knack-tactical/GAL/.ref/PCB Wire Diagram.png

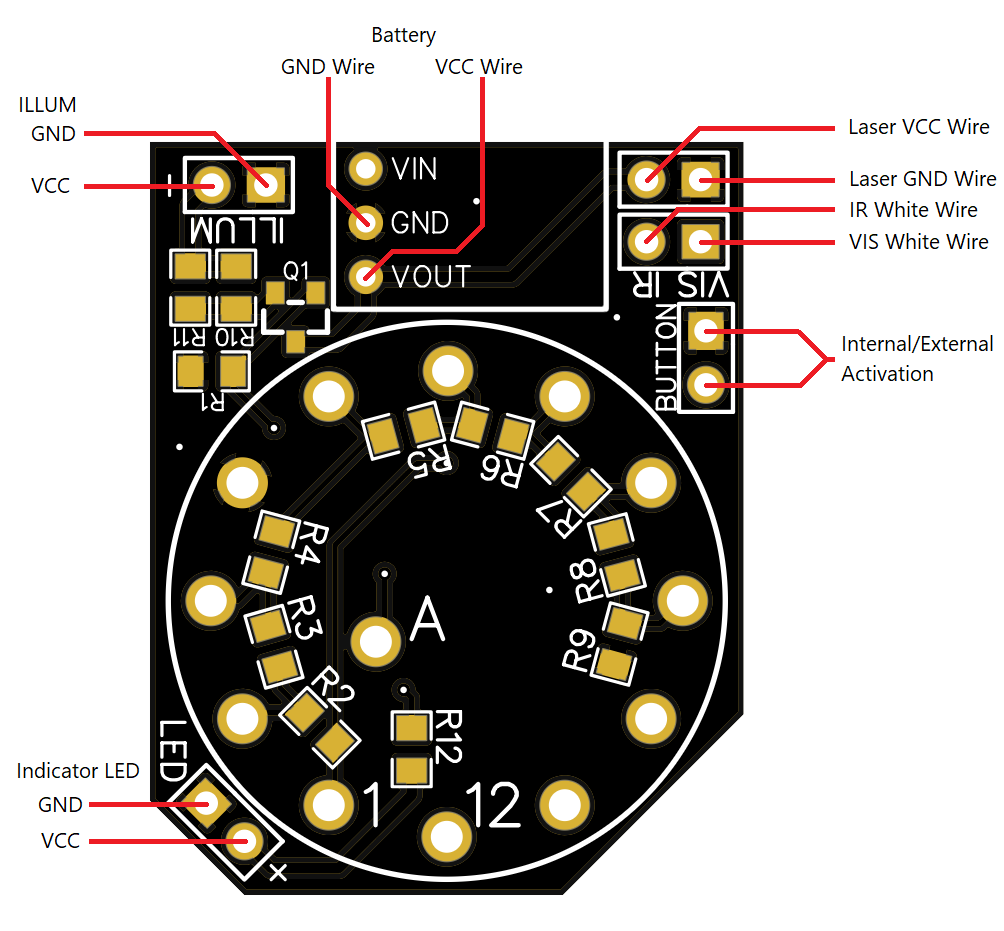
.ref/PCB Wire Diagram.png
