knack-tactical/GAL/attiny_program/Tools_settings.png

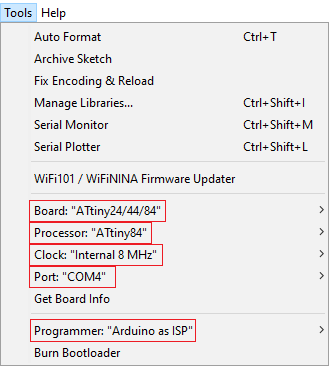
attiny_program/Tools_settings.png
