knack-tactical/GAL/RENDER/GAL_top.png

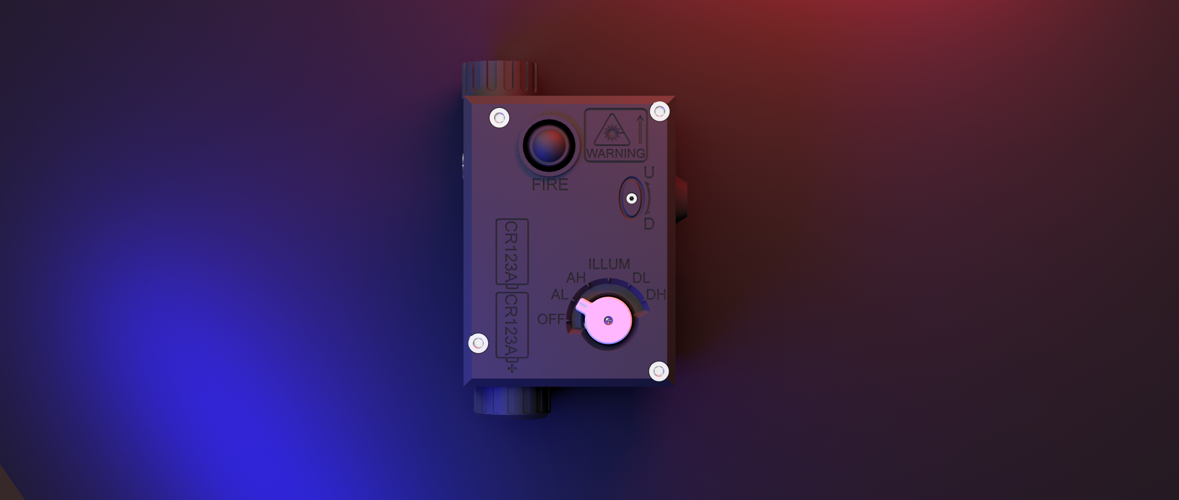
RENDER/GAL_top.png
