knack-tactical/GAL/Renders/2.png

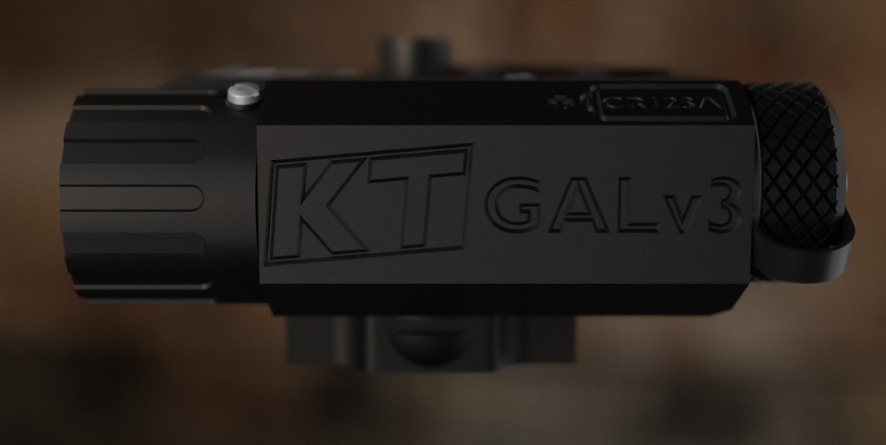
Renders/2.png
