knack-tactical/GAL/Renders/3.png

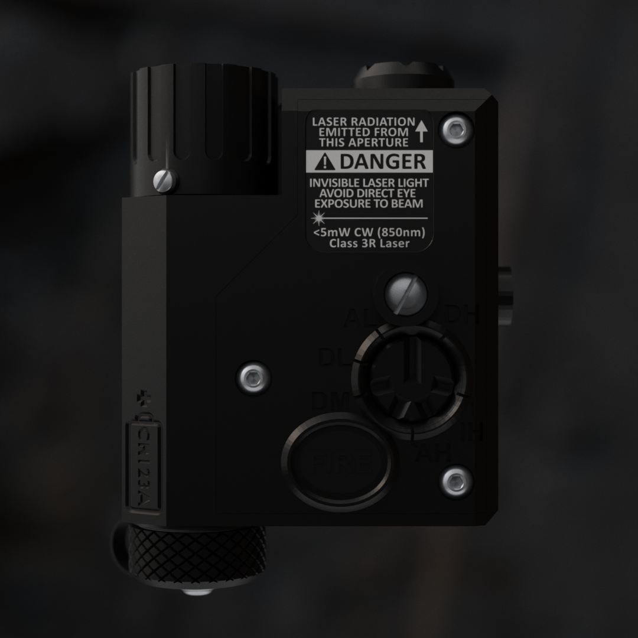
Renders/3.png
