knack-tactical/GAL/Renders/4.JPG

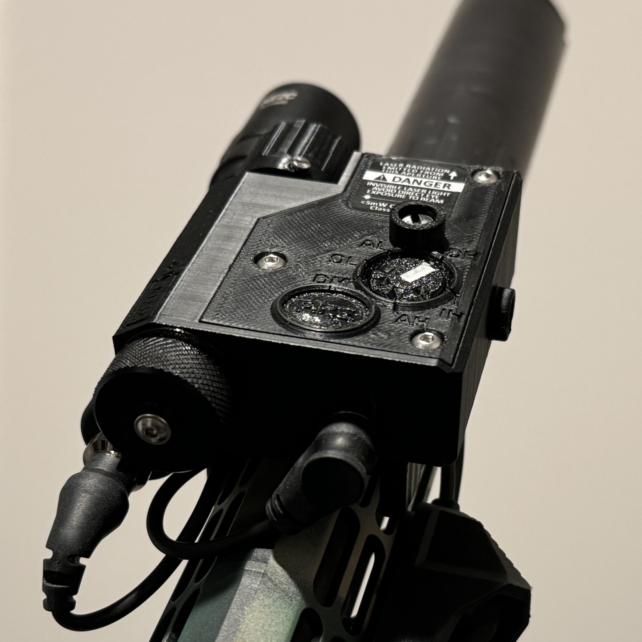
Renders/4.JPG
