knack-tactical/GAL/Renders/5.JPG

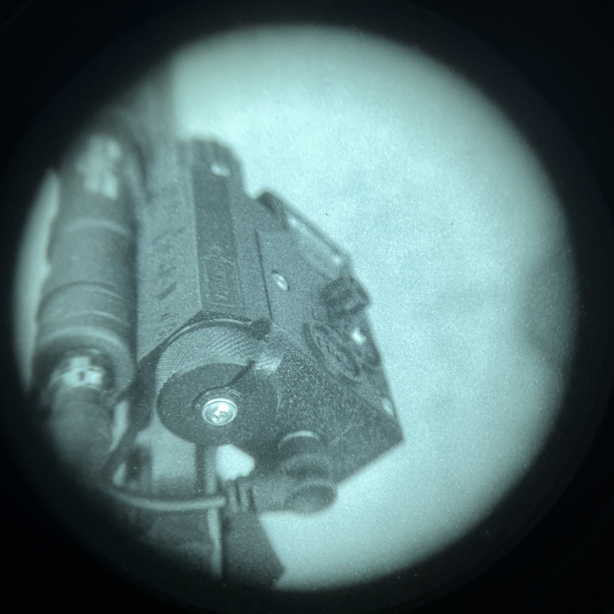
Renders/5.JPG
