knack-tactical/GAL/Renders/6.JPG

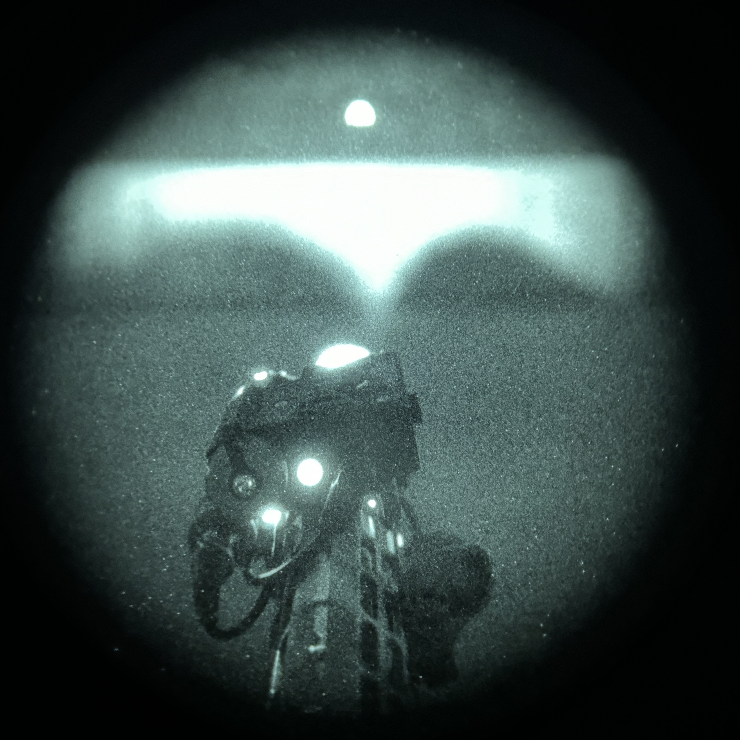
Renders/6.JPG
