knack-tactical/GAL/Renders/front_angle_warehouse.png

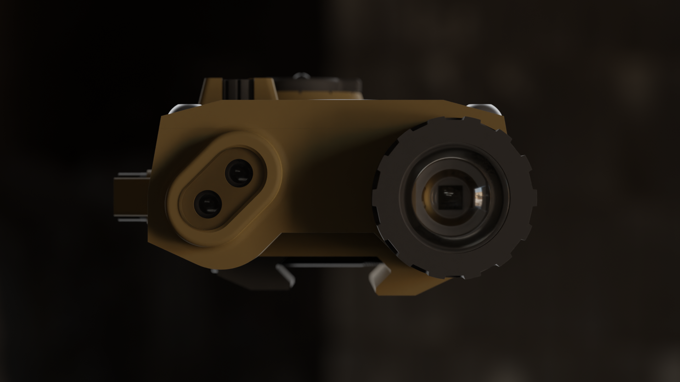
Renders/front_angle_warehouse.png
