knack-tactical/GAL/Renders/front_dark.png

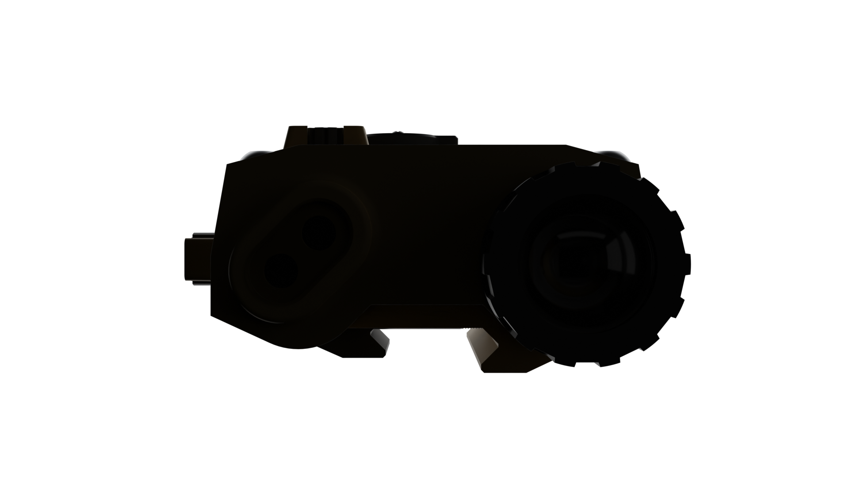
Renders/front_dark.png
