knack-tactical/GAL/Renders/illum_angle_warehouse.png

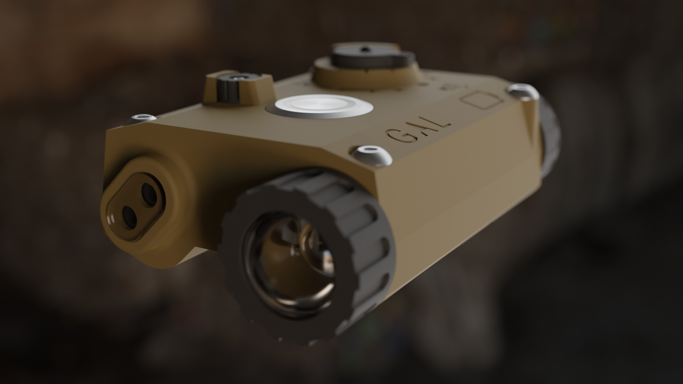
Renders/illum_angle_warehouse.png
