knack-tactical/GAL/Renders/render.png

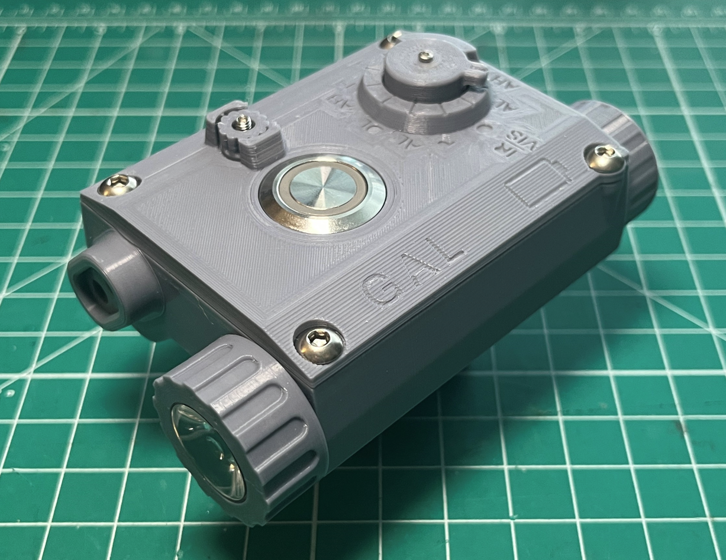
Renders/render.png
