knack-tactical/GAL/Machined Parts Drawings/battery_cap.PNG

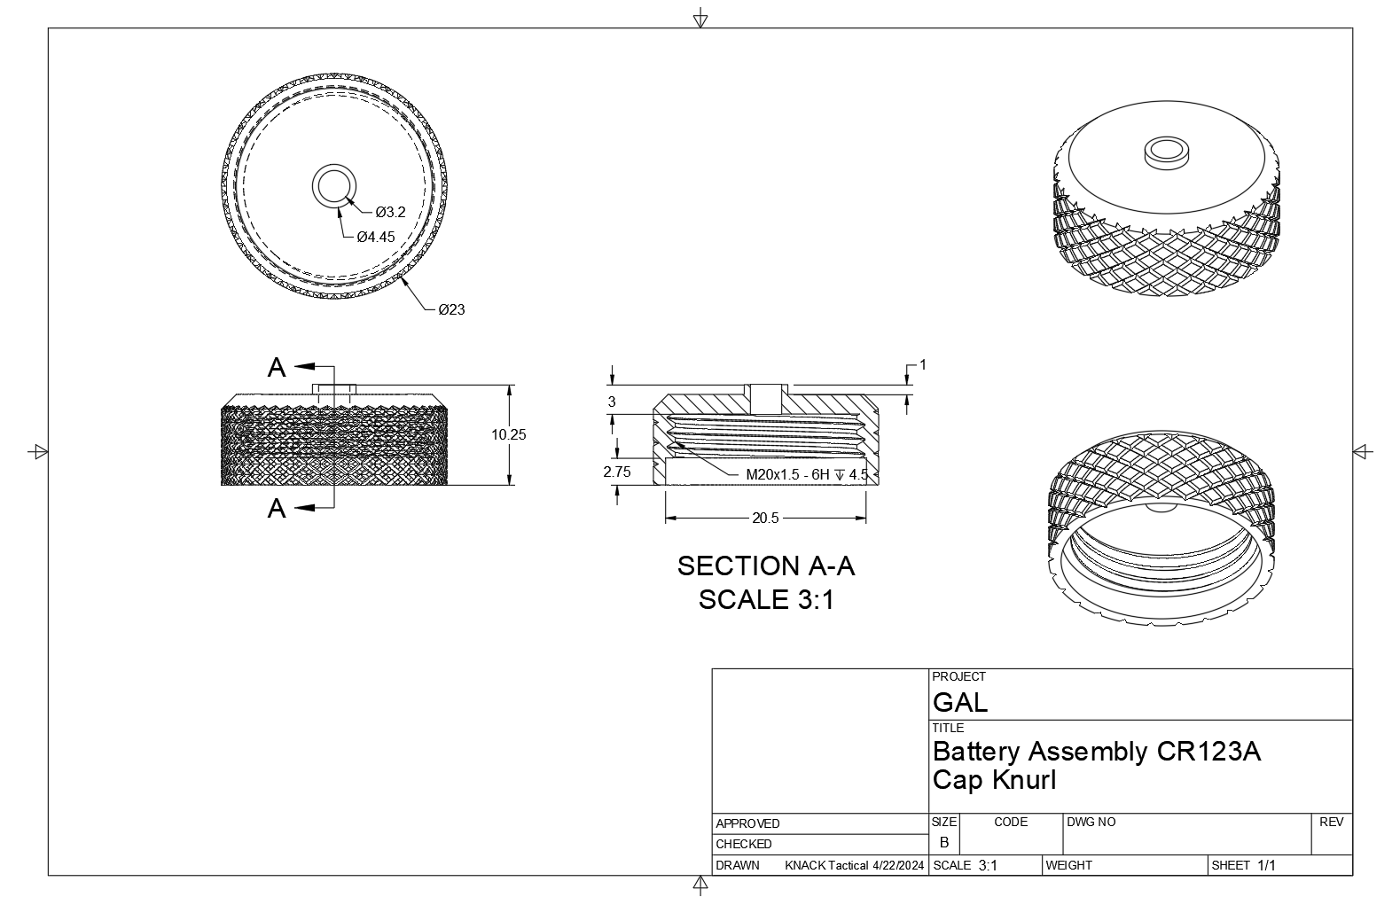
Machined Parts Drawings/battery_cap.PNG
