knack-tactical/GAL/Machined Parts Drawings/battery_tube.PNG

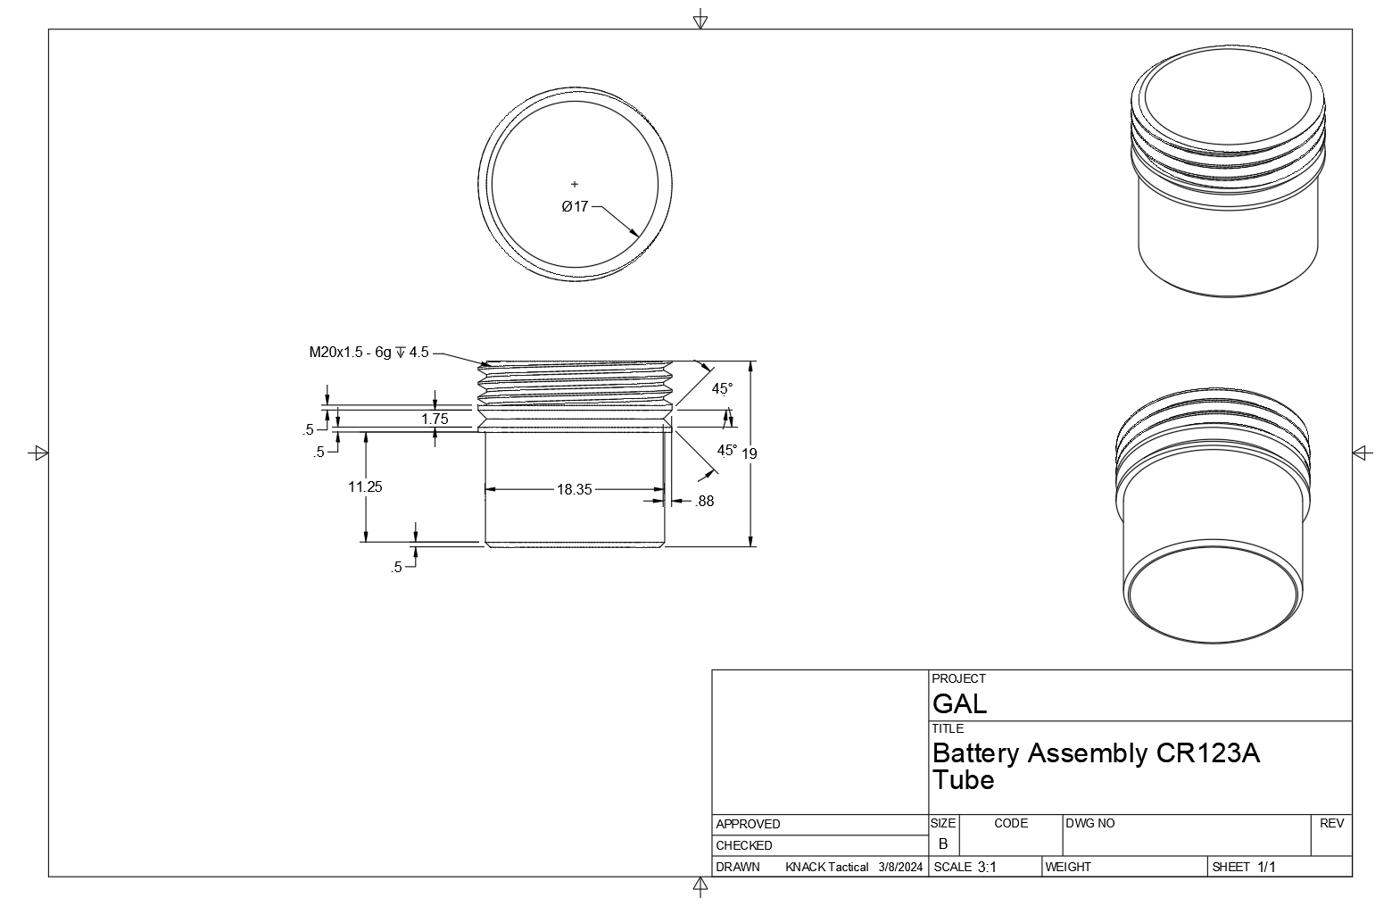
Machined Parts Drawings/battery_tube.PNG
