knack-tactical/GAL/Machined Parts Drawings/crane_port_stage_1.PNG

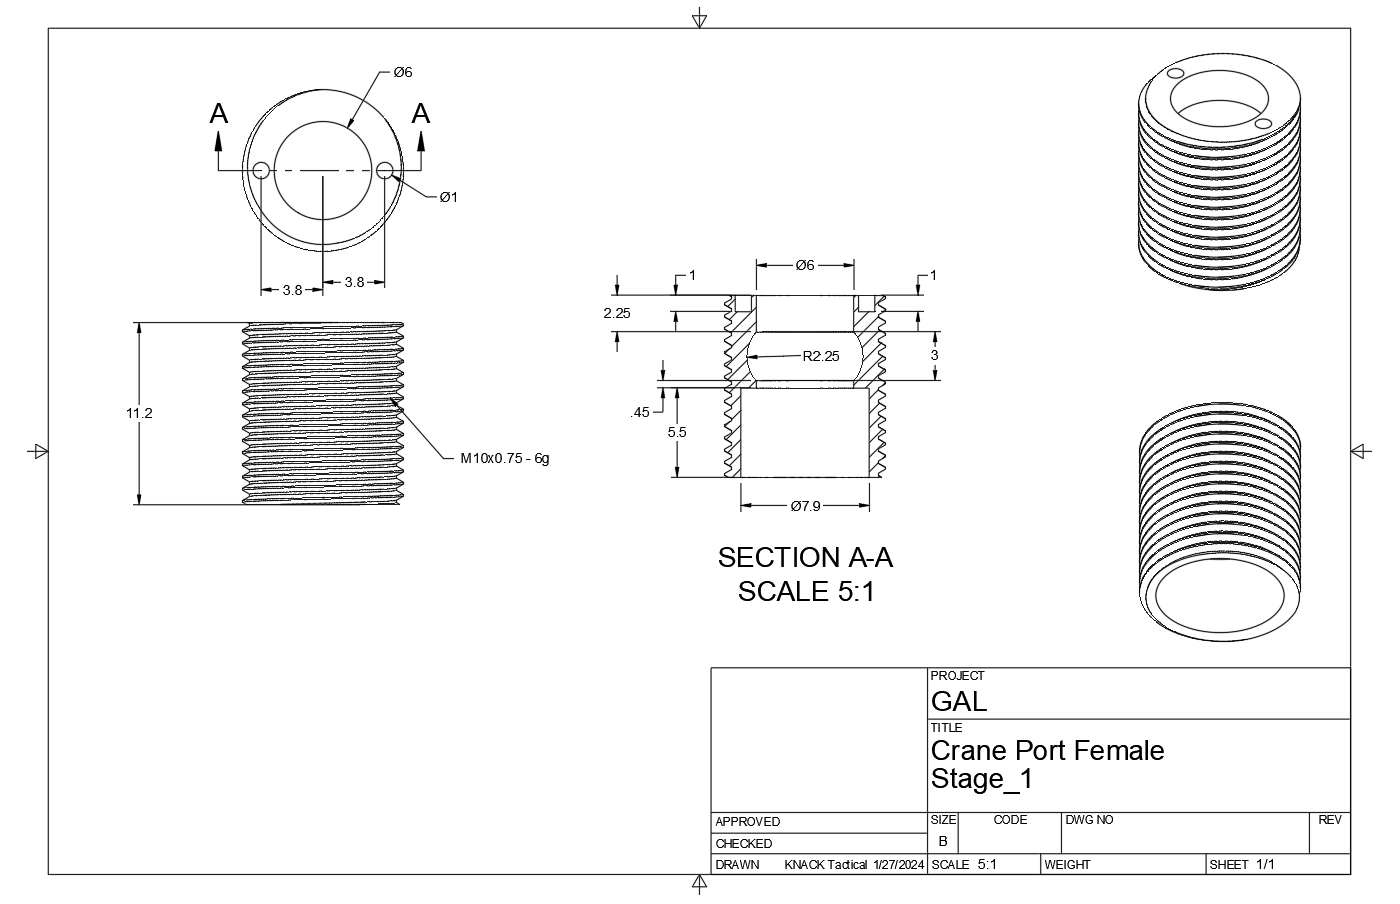
Machined Parts Drawings/crane_port_stage_1.PNG
