knack-tactical/GAL/Machined Parts Drawings/crane_port_stage_2.PNG

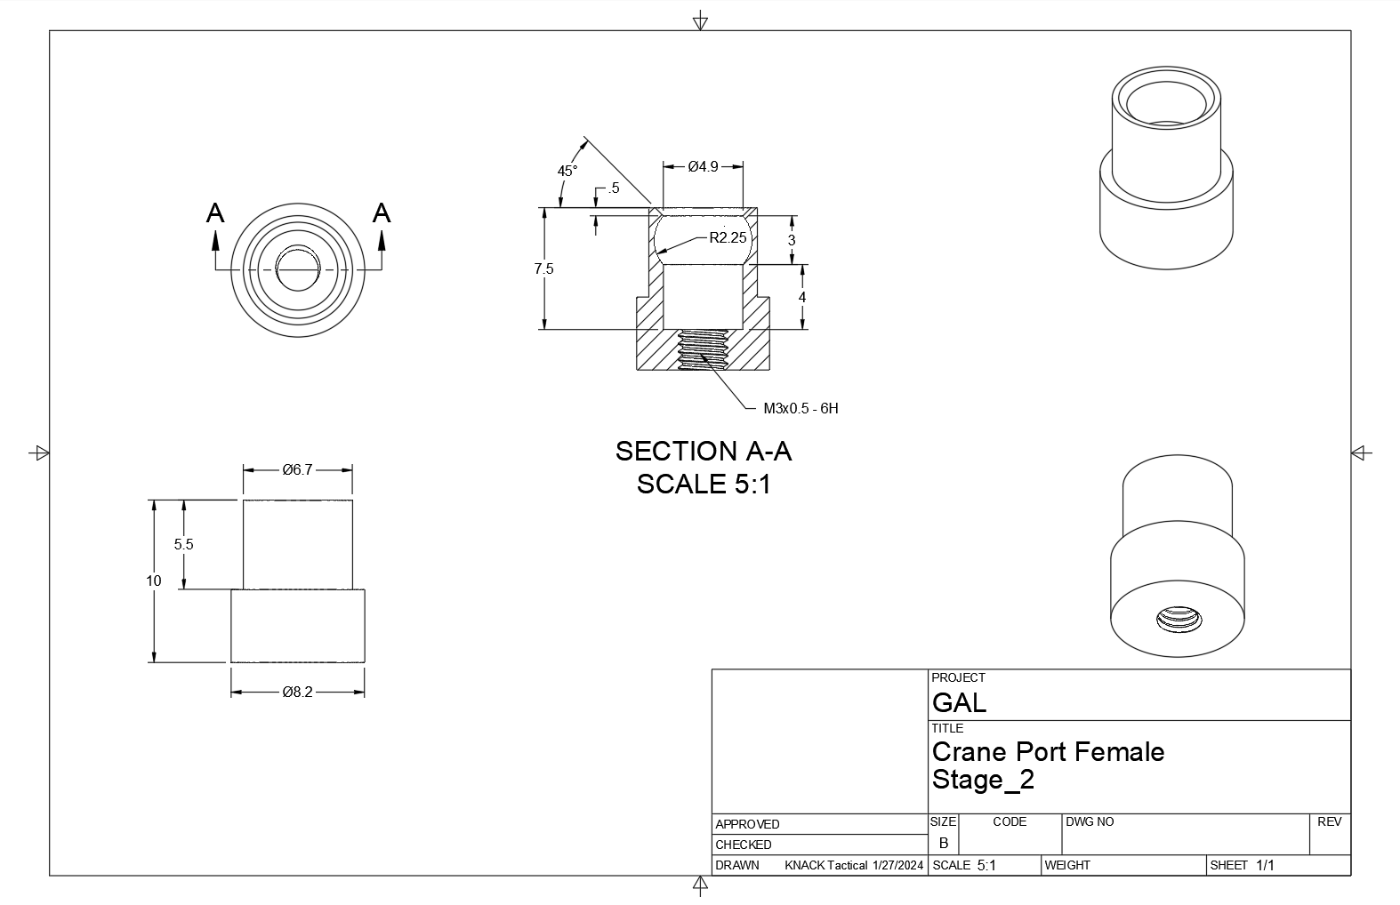
Machined Parts Drawings/crane_port_stage_2.PNG
