knack-tactical/GAL/STL/community_mods/mod_03_selector_knob.stl

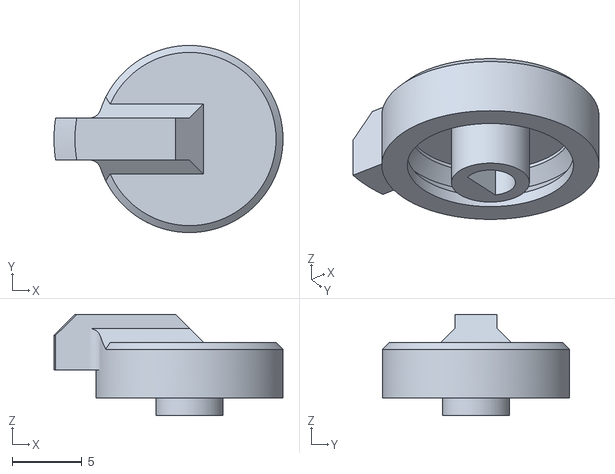
[picture p38: CAD file, 2024-10-04]
STL/community_mods/mod_03_selector_knob.stl
16.4 x 13.4 x 7.25
