knack-tactical/GAL/STEP/edits_by_zb/GAL_battery_cap_retention_zb.step

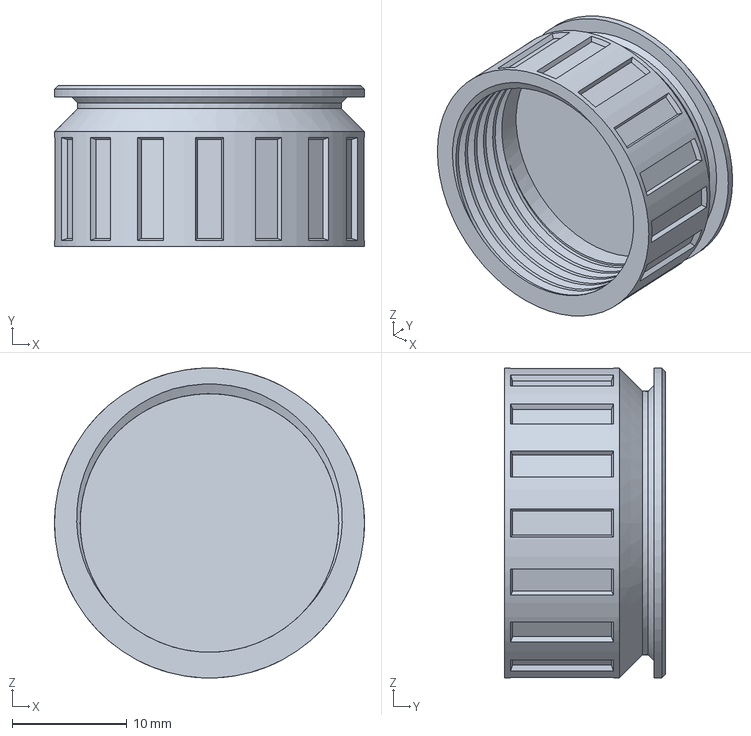
[picture p39: CAD file, 2023-12-14]
STEP/edits_by_zb/GAL_battery_cap_retention_zb.step
27.0 x 14.0 x 27.0 mm
