knack-tactical/GAL/STL/07_crane_port_spacer.stl

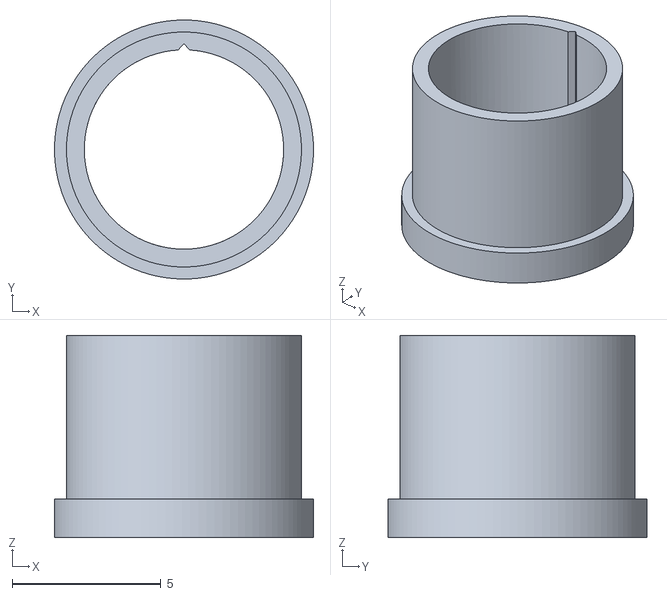
[picture p40: CAD file, 2024-07-04]
STL/07_crane_port_spacer.stl
8.71 x 8.71 x 6.80
