knack-tactical/GAL/STEP/edits_by_zb/GAL_TPU_gaskets_retention_zb.step

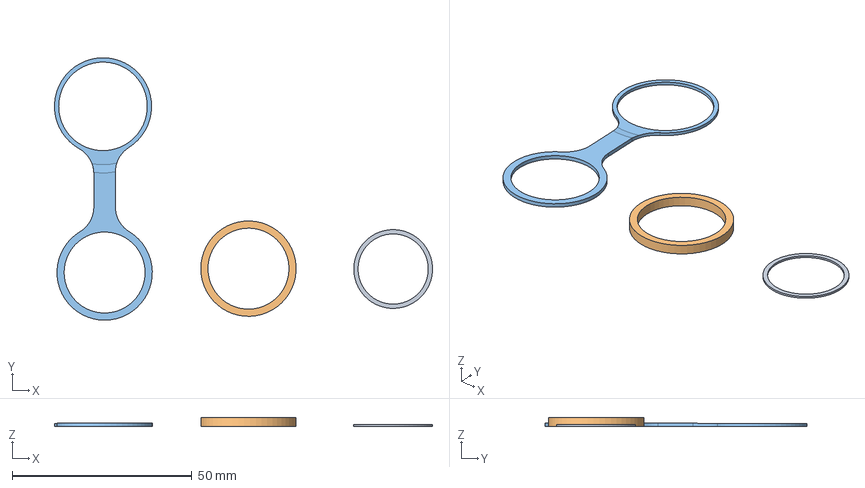
[picture p41: CAD file, 2023-12-14]
STEP/edits_by_zb/GAL_TPU_gaskets_retention_zb.step
105.0 x 72.9 x 2.50 mm
