knack-tactical/GAL/STL/community_mods/mod_01_selector_knob_zb.stl

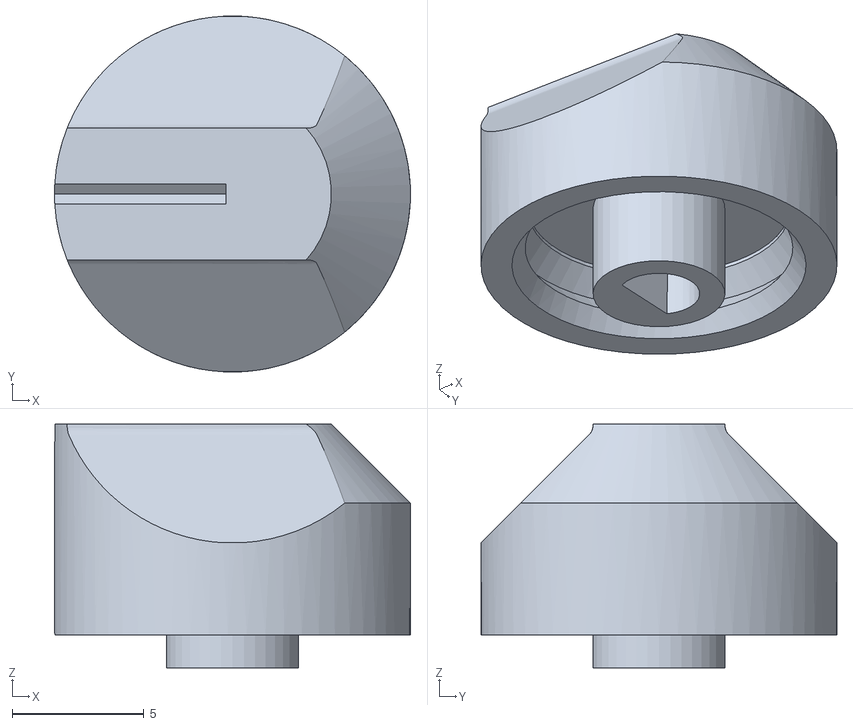
[picture p42: CAD file, 2024-08-01]
STL/community_mods/mod_01_selector_knob_zb.stl
13.5 x 13.5 x 9.25
