knack-tactical/GAL/STL/edits_by_zb/GAL_body_18650_crane_zb.stl

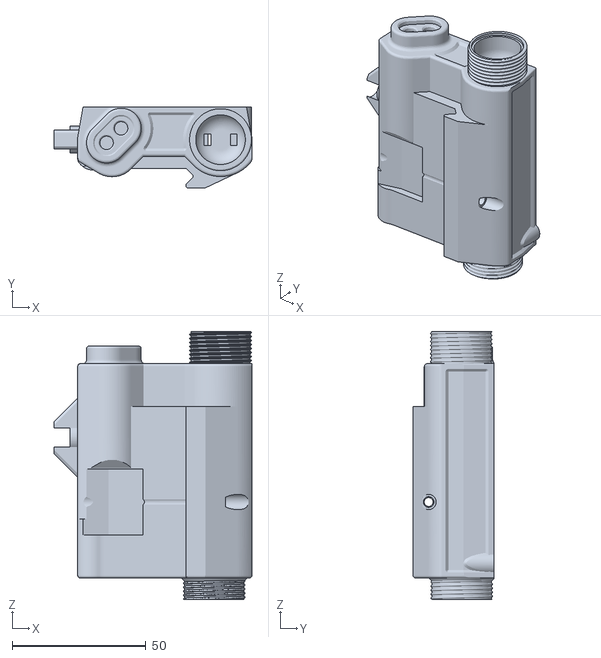
[picture p43: CAD file, 2023-12-15]
STL/edits_by_zb/GAL_body_18650_crane_zb.stl
73.8 x 30.2 x 100.0
