knack-tactical/GAL/STL/04_laser_lens_cap.stl

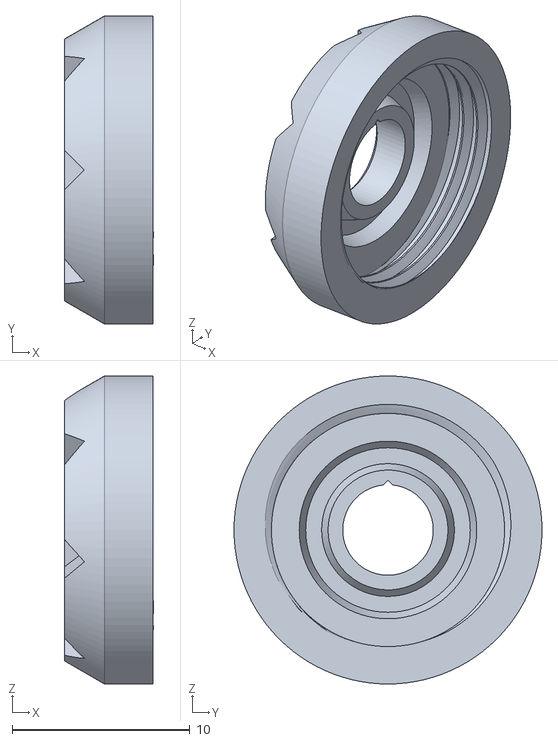
[picture p44: CAD file, 2024-07-03]
STL/04_laser_lens_cap.stl
5.02 x 17.3 x 17.3
