knack-tactical/GAL/STL/08_crane_port_installation_tool.stl

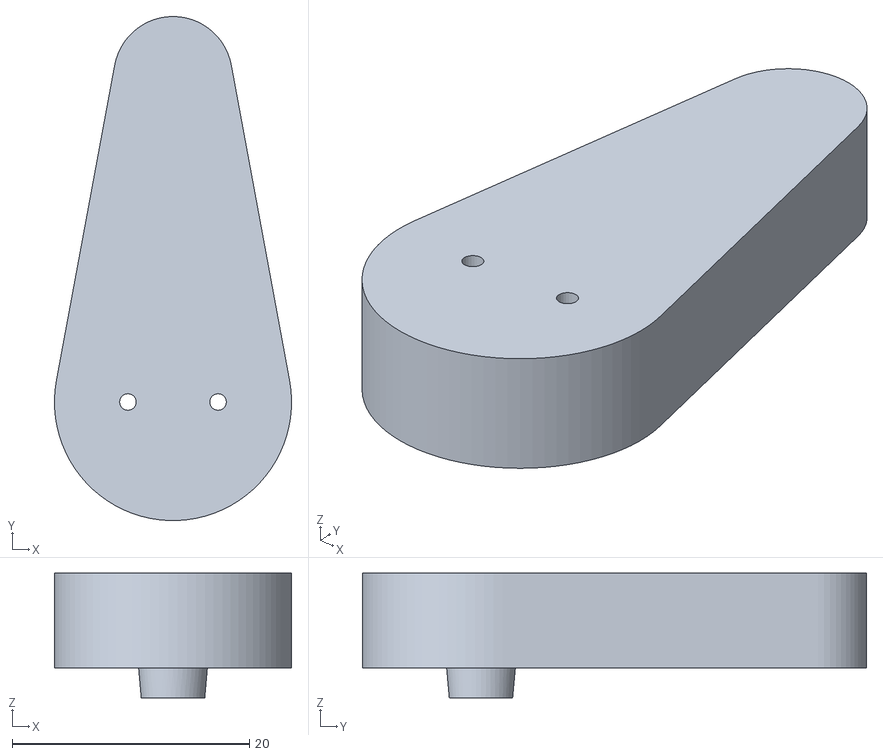
[picture p45: CAD file, 2024-07-03]
STL/08_crane_port_installation_tool.stl
20.0 x 42.5 x 10.5
