knack-tactical/GAL/STL/03_laser_housing.stl

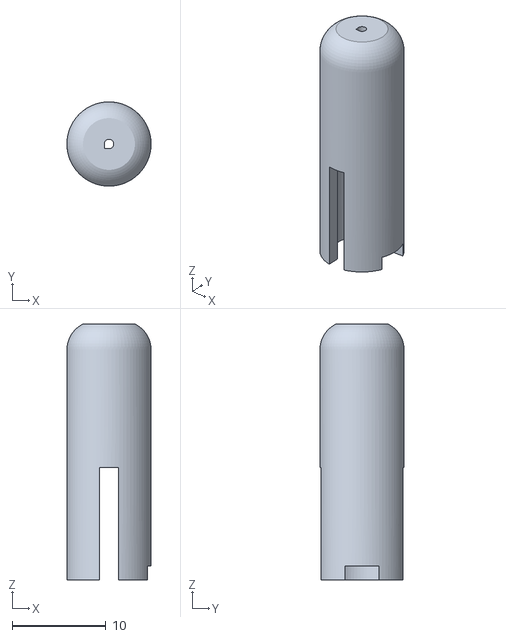
[picture p46: CAD file, 2024-07-03]
STL/03_laser_housing.stl
9.00 x 9.00 x 27.4
