knack-tactical/GAL/STL/09_battery_cap_retention_strap_TPU.stl

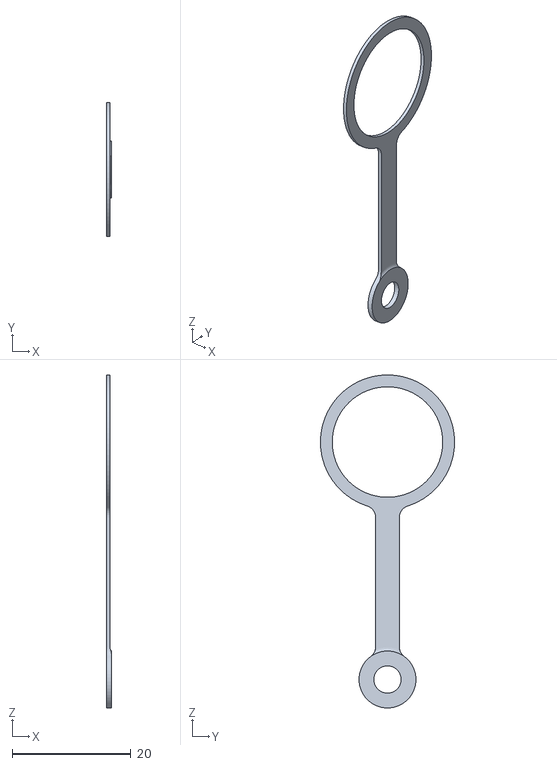
[picture p47: CAD file, 2024-07-03]
STL/09_battery_cap_retention_strap_TPU.stl
0.85 x 22.6 x 56.1
