knack-tactical/GAL/STL/02_laser_base.stl

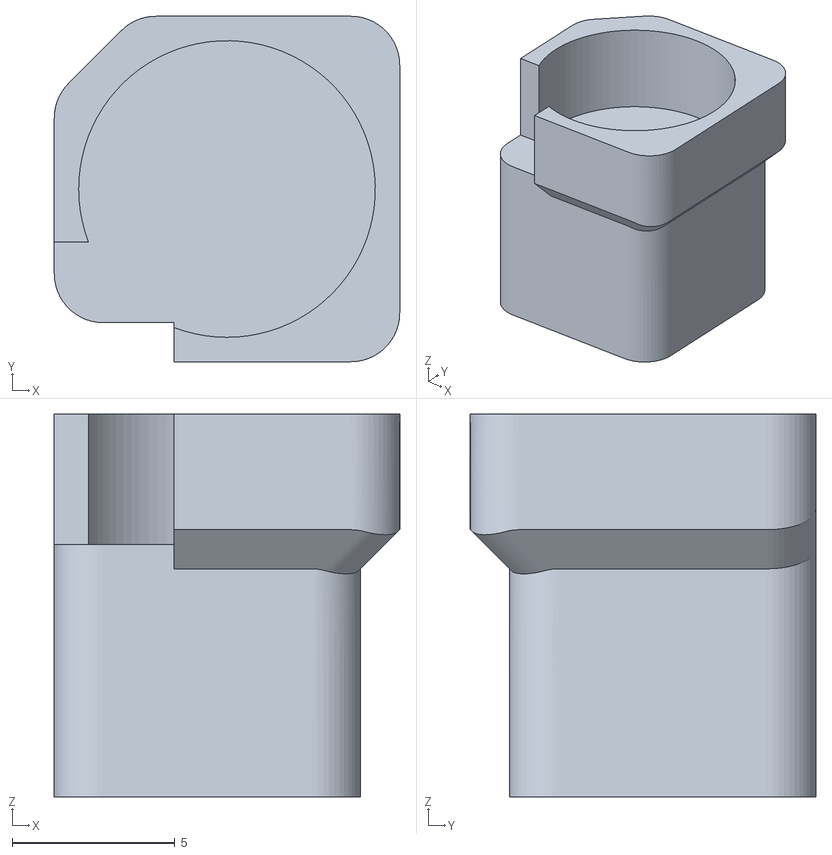
[picture p48: CAD file, 2024-07-03]
STL/02_laser_base.stl
10.6 x 10.6 x 11.8
