knack-tactical/GAL/STL/14_FIRE_button_TPU.stl

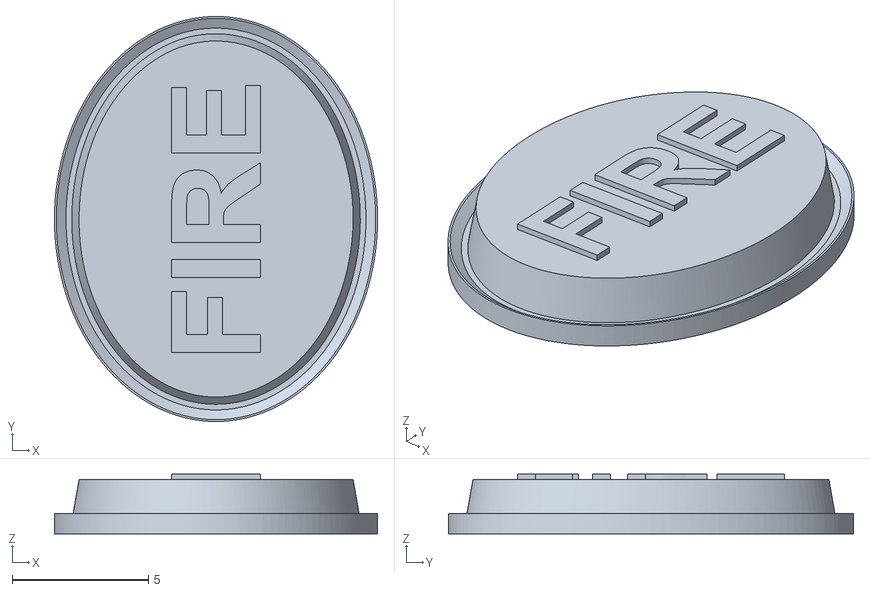
[picture p49: CAD file, 2024-07-03]
STL/14_FIRE_button_TPU.stl
11.9 x 14.9 x 2.20
