knack-tactical/GAL/STL/05_lens_cap.stl

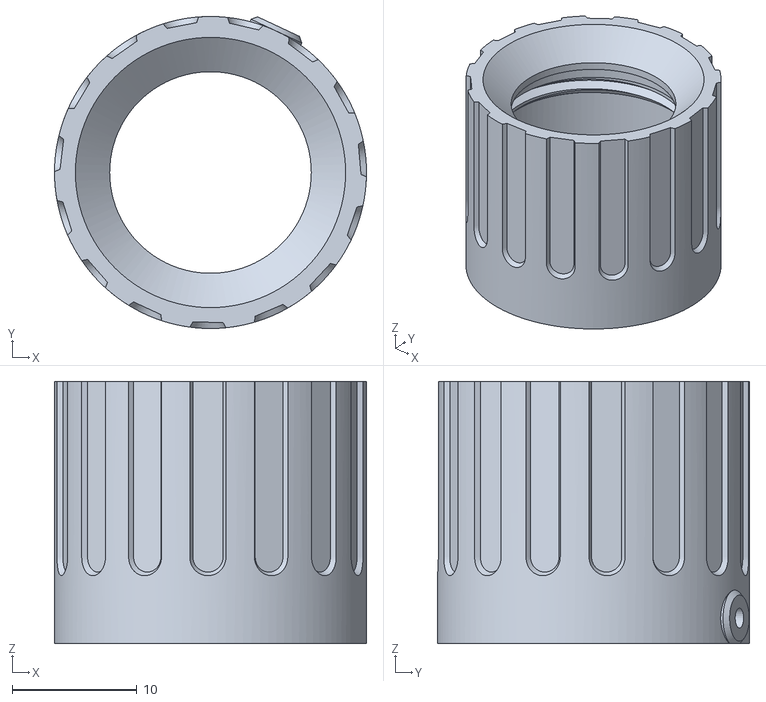
[picture p50: CAD file, 2024-07-03]
STL/05_lens_cap.stl
25.0 x 25.0 x 21.0
