knack-tactical/GAL/STL/13_button_retainer.stl

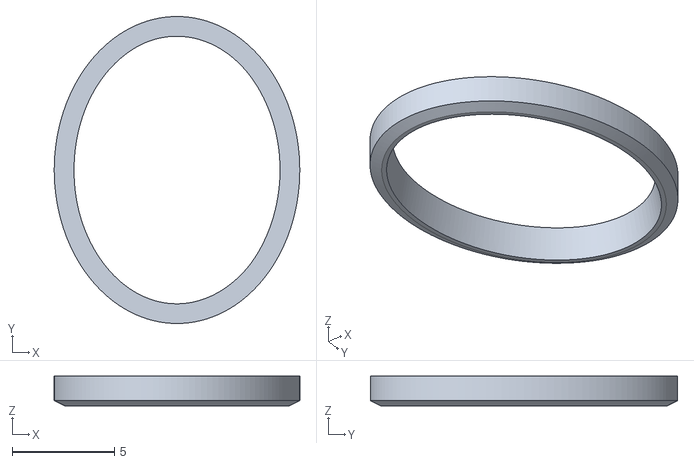
[picture p51: CAD file, 2024-07-03]
STL/13_button_retainer.stl
12.0 x 15.0 x 1.45
