knack-tactical/GAL/STL/06_lens_locking_ring.stl

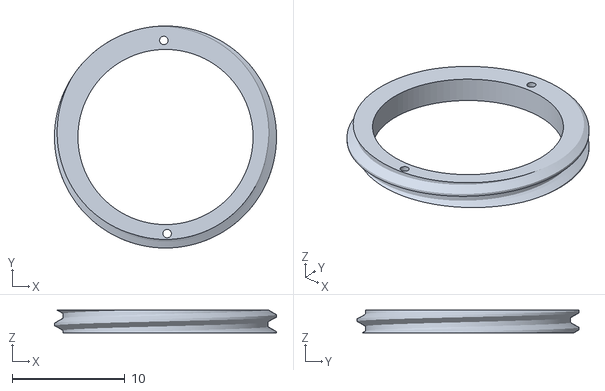
[picture p52: CAD file, 2024-07-03]
STL/06_lens_locking_ring.stl
19.6 x 19.6 x 2.00
