knack-tactical/GAL/STL/battery_cap.stl

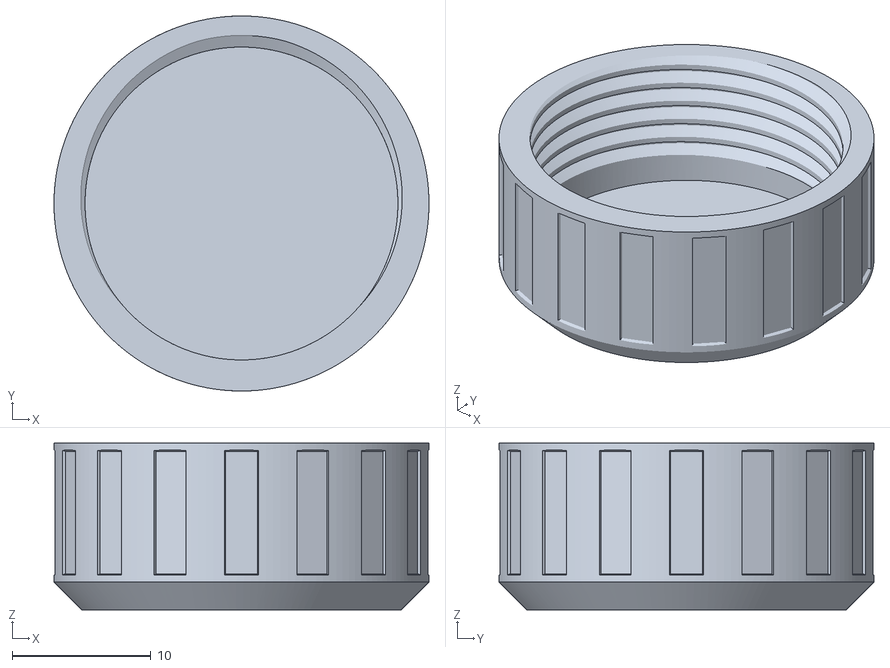
[picture p53: CAD file, 2023-12-23]
STL/battery_cap.stl
27.0 x 27.0 x 12.0
