knack-tactical/GAL/STL/vertical_adjustment_support.stl

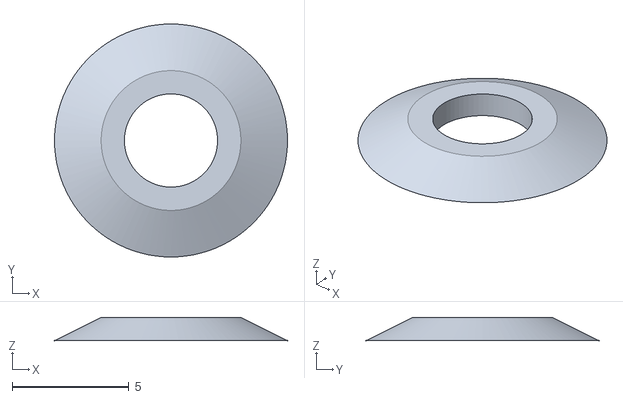
[picture p54: CAD file, 2023-10-02]
STL/vertical_adjustment_support.stl
10.0 x 10.0 x 1.00
