knack-tactical/GAL/STL/rotary_switch_jig.stl

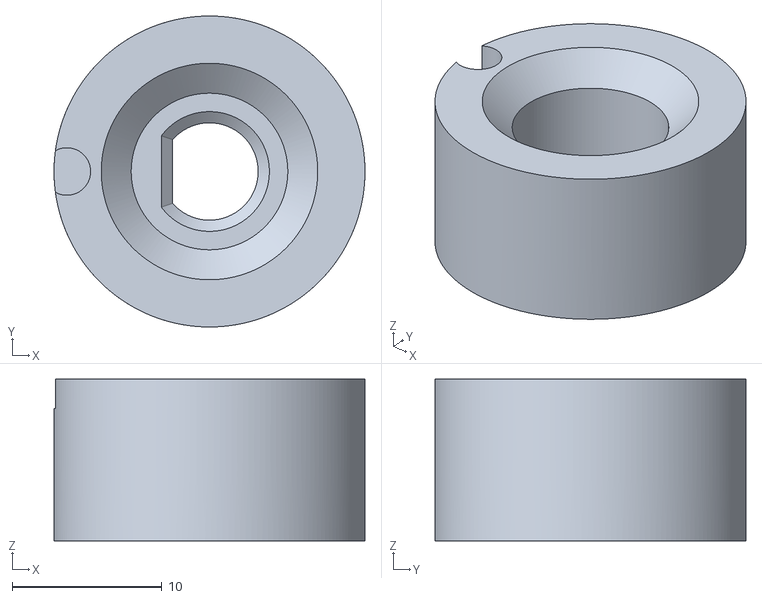
[picture p55: CAD file, 2023-10-02]
STL/rotary_switch_jig.stl
20.8 x 20.8 x 10.8
