knack-tactical/GAL/STL/adjustment_locking_knob.stl

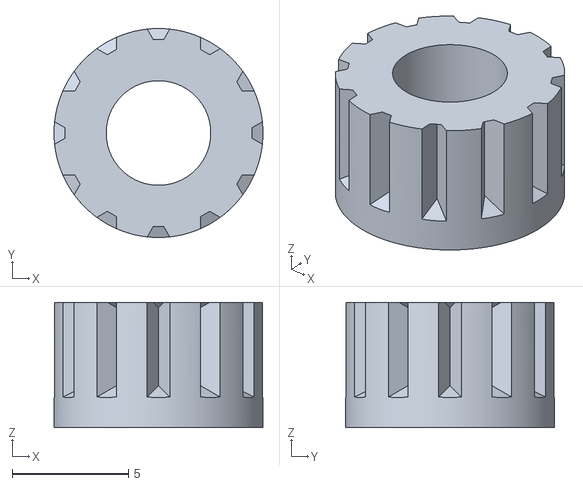
[picture p56: CAD file, 2023-10-02]
STL/adjustment_locking_knob.stl
9.00 x 9.00 x 5.40
