knack-tactical/GAL/STL/laser_hole_cover.dxf

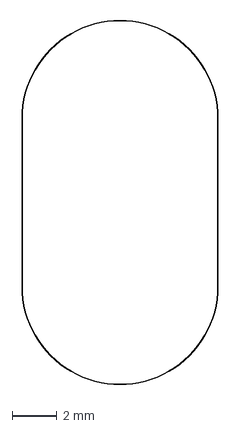
[picture p57: CAD file, 2023-10-02]
STL/laser_hole_cover.dxf
8.75 x 16.6 mm
