knack-tactical/GAL/STL/lid.stl

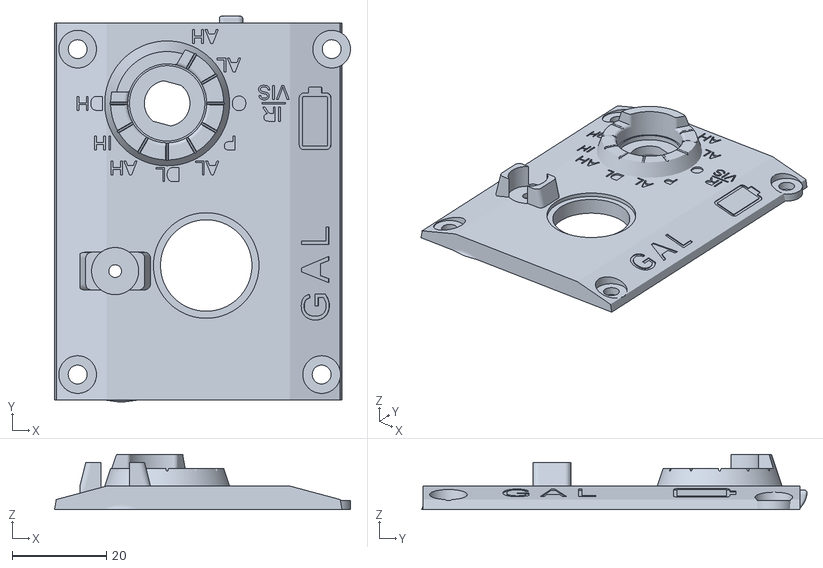
[picture p58: CAD file, 2023-10-02]
STL/lid.stl
62.8 x 81.9 x 11.8
