knack-tactical/GAL/STL/pic_rail_clamp.stl

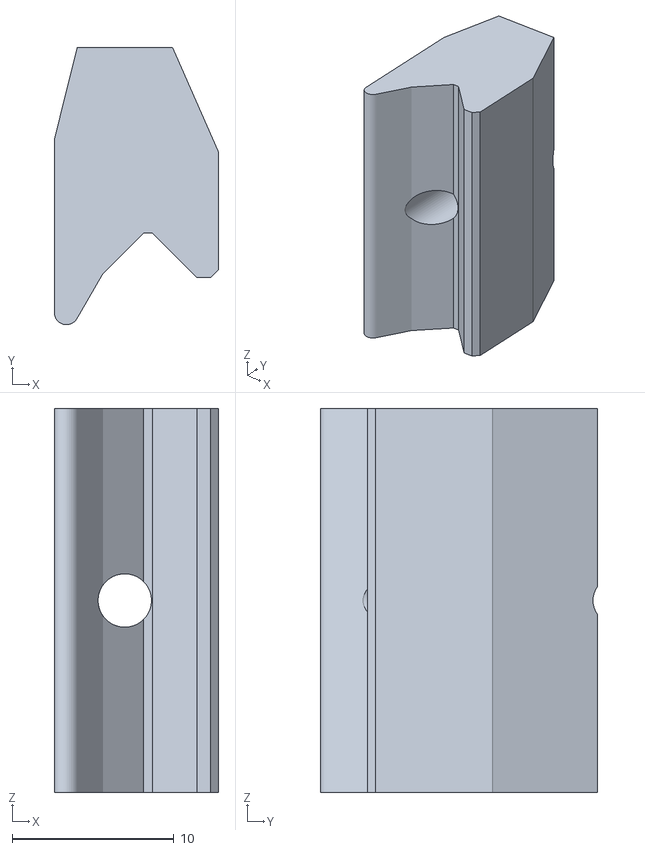
[picture p59: CAD file, 2023-10-02]
STL/pic_rail_clamp.stl
10.2 x 17.2 x 23.8
