knack-tactical/GAL/STL/Laser Body.stl

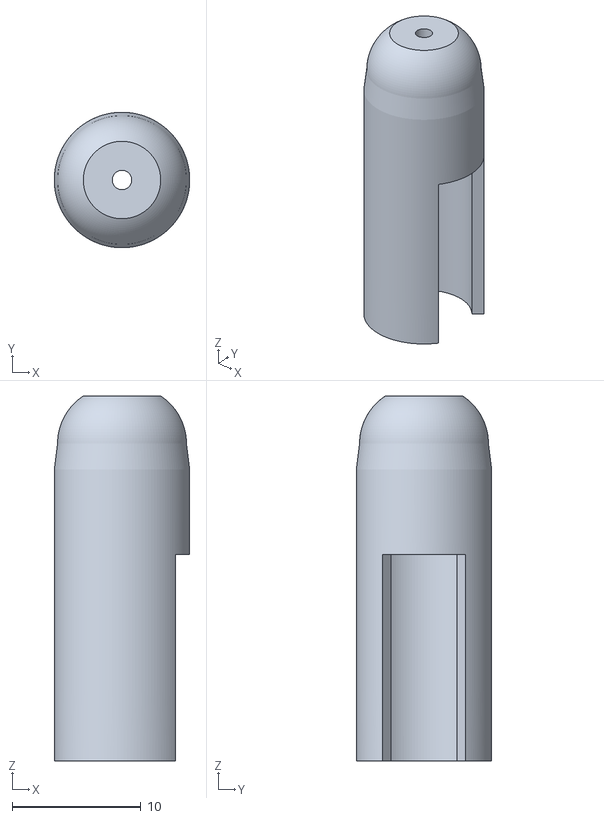
[picture p60: CAD file, 2023-03-20]
STL/Laser Body.stl
10.5 x 10.5 x 28.3
