knack-tactical/GAL/STL/Laser Base.stl

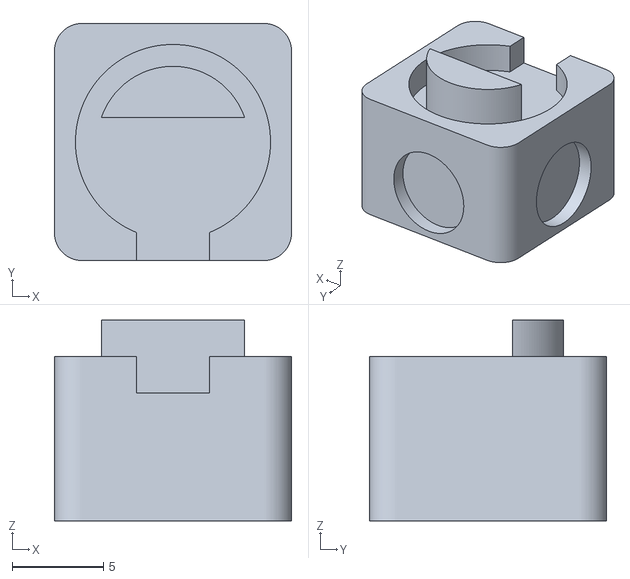
[picture p61: CAD file, 2023-03-20]
STL/Laser Base.stl
13.0 x 13.0 x 11.0
