knack-tactical/GAL/STL/GAL Rail Mount.stl

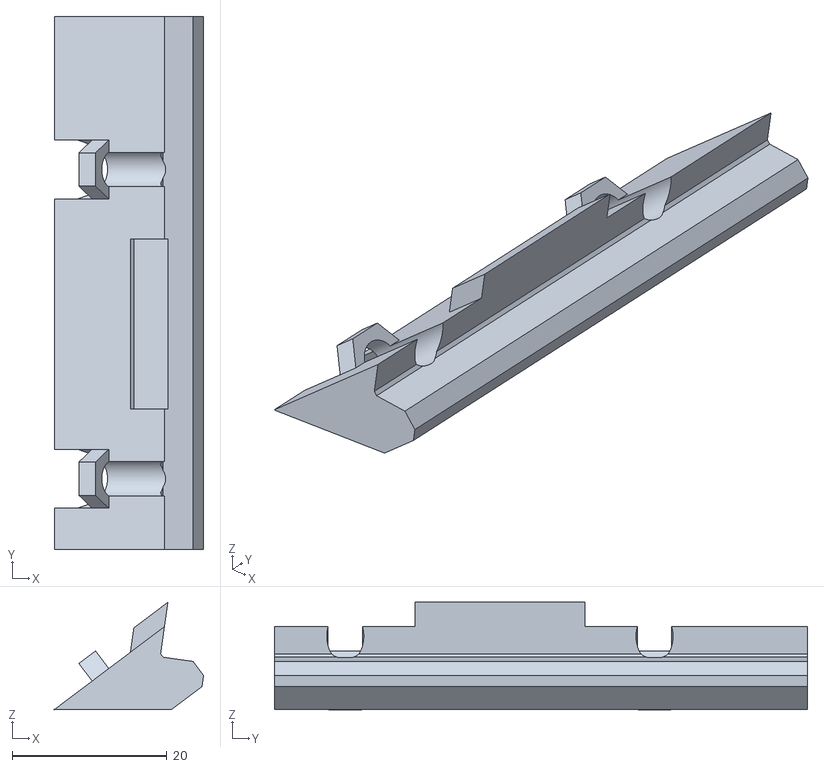
[picture p62: CAD file, 2023-03-08]
STL/GAL Rail Mount.stl
19.3 x 69.0 x 13.9
