knack-tactical/GAL/STL/Selector Cap.stl

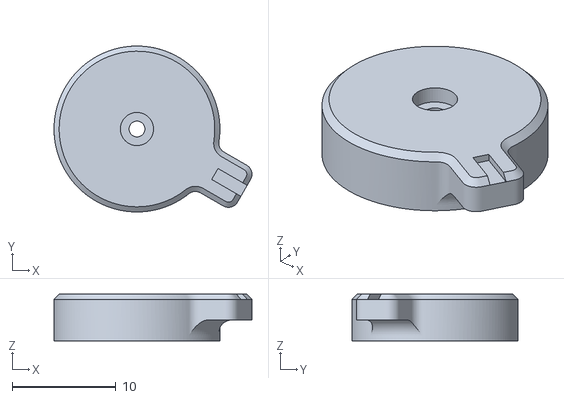
[picture p63: CAD file, 2023-03-08]
STL/Selector Cap.stl
19.1 x 16.0 x 4.50
