knack-tactical/GAL/Wiring Diagram.png

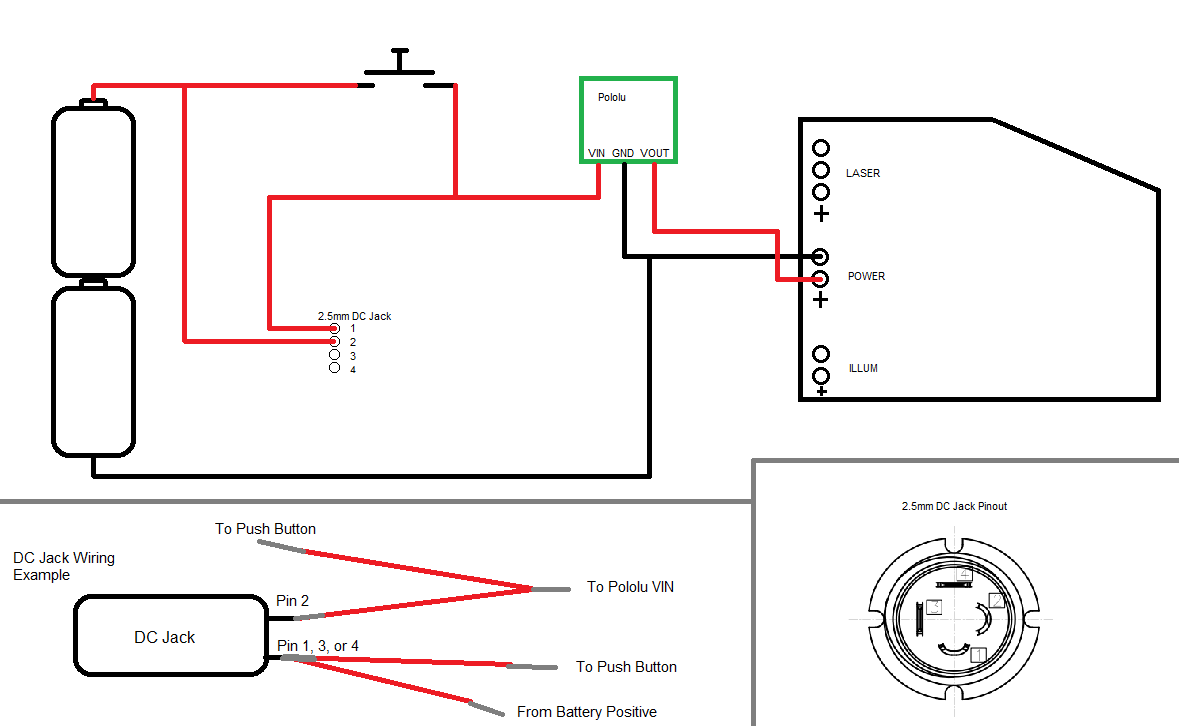
Wiring Diagram.png
